ryanchaiyakul/potentiostat/CAD/LTSpice/Control Amp/ADA4622/Control Amp ADA4625 (Experimental).asc

R1: res; 10000
R2: res; 46392
U1: ADA4622
V1: voltage; 0
V2: voltage; 5
Named nets: 0, 5V, CE, DAC_OUT, RE
.dc V1 0 3.3 0.01
