ryanchaiyakul/potentiostat/CAD/LTSpice/Control Amp/ADA4622/Control AMP ADA4625 Transient (Experimental).asc

R1: res; 10000
R2: res; 46392
U1: ADA4622
V1: voltage; PWL file=swv.txt
V2: voltage; 5
Named nets: 0, 5V, CE, DAC_OUT, RE
.tran 0 9 0 0.01
