ryanchaiyakul/potentiostat/CAD/LTSpice/Control Amp/LT1462/Control Amp LT1462 Transients (Experimental).asc

R1: res; 10000
R2: res; 46392
U1: LT1462
V1: voltage; 3.3
V2: voltage; PWL file=swv.txt
Named nets: 0, 3.3V, RE, CE, DAC_OUT
.tran 0 9 0 0.01
