ryanchaiyakul/potentiostat/CAD/LTSpice/CPE/Randles Tester/cpe1.asc

C1: cap; 2.3655090766818945m
C2: cap; 1.4274608509243711m
C3: cap; 861.3978703391572u
C4: cap; 519.8085051119542u
C5: cap; 313.67721153099507u
C6: cap; 189.28777052747355u
C7: cap; 114.22525690145986u
C8: cap; 68.92896079787036u
C9: cap; 41.595018173372345u
C10: cap; 25.100415221937176u
C11: cap; 15.146786129233593u
C12: cap; 9.140292222904383u
C13: cap; 5.515687698187207u
C14: cap; 3.328428680616806u
C15: cap; 2.0085324057766334u
C16: cap; 1.212044124168307u
C17: cap; 731.405156673529n
C18: cap; 441.364709866243n
C19: cap; 671.6401428134171n
R1: res; 6.412486486066959meg
R2: res; 4.22741983895789meg
R3: res; 1.67962742799552meg
R4: res; 667.3451902923115k
R5: res; 265.14785099560146k
R6: res; 105.34785282080367k
R7: res; 41.856534202639345k
R8: res; 16.630329034202642k
R9: res; 6.607518970560247k
R10: res; 2.625282209180706k
R11: res; 1.043070282287264k
R12: res; 414.4299648952302
R13: res; 164.66023308270306
R14: res; 65.42237447937526
R15: res; 25.993447248248913
R16: res; 10.327648686314557
R17: res; 4.103354448114615
R18: res; 1.6303340903892138
R19: res; 647.760089920212m
Named nets: A, B
