ryanchaiyakul/potentiostat/CAD/LTSpice/CPE/Randles Tester/cpe2.asc

C1: cap; 181.21604919389156n
C2: cap; 163.35222877831924n
C3: cap; 147.24937865902783n
C4: cap; 132.73390683205375n
C5: cap; 119.64933355472706n
C6: cap; 107.85460446217489n
C7: cap; 97.22256997253973n
C8: cap; 87.63861458859019n
C9: cap; 78.9994213193171n
C10: cap; 71.21185790172778n
C11: cap; 64.19197281608272n
C12: cap; 57.8640902714143n
C13: cap; 52.15999440508718n
C14: cap; 47.01819390190557n
C15: cap; 42.383259105211465n
C16: cap; 38.20522447389643n
C17: cap; 34.43904994369196n
C18: cap; 31.044135386103342n
C19: cap; 283.8770536114015n
R1: res; 152.28690451341373g
R2: res; 55.18275033852288g
R3: res; 14.677500365520673g
R4: res; 3.9039195338813926g
R5: res; 1.03836398211393g
R6: res; 276.18390952836046meg
R7: res; 73.45935837169706meg
R8: res; 19.53871006314831meg
R9: res; 5.196903422435292meg
R10: res; 1.3822716594305113meg
R11: res; 367.6564263665744k
R12: res; 97.78920585287135k
R13: res; 26.009959558820995k
R14: res; 6.918125475621083k
R15: res; 1.8400820650336644k
R16: res; 489.42477525020337
R17: res; 130.17713458575
R18: res; 34.62449640048013
R19: res; 9.209418803093675
Named nets: A, B
