ryanchaiyakul/potentiostat/CAD/LTSpice/CPE/Randles Tester/randles.asc

R1: res; 230
R2: res; 37.785k
X1: cpe1
X2: cpe2
Named nets: A, B
