ryanchaiyakul/potentiostat/CAD/LTSpice/CPE/Randles Tester/Randles_Tester.asc

B1: bv; V=1-V(re)
V1: voltage; PWL file=swv.txt
X1: randles
Named nets: 0, RE, WE-RE
.tran 0 11 0 0.01
