ryanchaiyakul/potentiostat/CAD/LTSpice/System/Mixed System.asc

B1: bv; V=2*V(dac_we)-V(re)
V1: voltage; 5
V2: voltage; PWL file=swv.txt
V4: voltage; 2
X1: OPA2328_Control_Amp
X2: OPA2328_Trans_Amp; R=2k C=1.5n
X3: randles
Named nets: 0, 5V, DAC_OUT, CE, RE, WE-RE, WE-I, SIG_OUT, DAC_WE
.tran 0 11 0
