ryanchaiyakul/potentiostat/CAD/LTSpice/System/OPA2328_Control_Amp.asc

R1: res; 46392
R2: res; 10000
U1: opamp2; OPAx328
Named nets: V+, 0, DAC_OUT, RE, CE
.inc OPAx328.LIB
