ryanchaiyakul/potentiostat/CAD/LTSpice/System/OPA2328_Trans_Amp.asc

C1: cap; {C}
R1: res; {R}
U1: opamp2; OPAx328
Named nets: 0, V+, WE, I, SIG_OUT
.inc OPAx328.LIB
