ryanchaiyakul/potentiostat/CAD/LTSpice/System/OPA2392_System.asc

B1: bv; V=2*V(dac_we)-V(re)
Control: OPA2392_Control_Amp
Randles: Randles_Circuit
Transimpedance: OPA2392_Trans_Amp; R=47k C=17nF
V1: voltage; 5
V2: voltage; PWL file=swv.txt
V4: voltage; 1
Named nets: 0, 5V, DAC_OUT, CE, RE, WE-RE, WE-I, SIG_OUT, DAC_WE
.tran 0 11 0
