ryanchaiyakul/potentiostat/CAD/LTSpice/System/OPA2392_Trans_Amp.asc

C1: cap; {C}
R1: res; {R}
U1: opamp2; OPAx392
Named nets: 0, V+, WE, I, SIG_OUT
.inc OPAx392.LIB
