ryanchaiyakul/potentiostat/CAD/LTSpice/Control Amp/ADA4622/Control AMP ADA4625 Noise.asc

R1: res; {CERE}
R2: res; {REWE}
U1: ADA4622
V1: voltage; PWL file=swv.txt
V2: voltage; 5
Named nets: 0, 5V, CE, DAC_OUT, RE
.step param REWE  list 5000 10000 100000
.step param CERE  list 1 1000 5000
.noise V(RE) V2 oct 100 100 100000
;tran 0 9 0 0.01
