ryanchaiyakul/potentiostat/CAD/LTSpice/Control Amp/LT1462/Control Amp LT1462 Transients.asc

R1: res; {C}
R2: res; {R}
U1: LT1462
V1: voltage; 3.3
V2: voltage; PWL file=swv.txt
Named nets: 0, 3.3V, RE, CE, DAC_OUT
.step param R list 5000 10000 100000
.step param C list 1 1000 5000
.tran 0 9 0 0.01
