ryanchaiyakul/potentiostat/CAD/LTSpice/Control Amp/OPA2392/OPA2392_Control_Amp.asc

R1: res; 46392
R2: res; 10000
U1: opamp2; OPAx392
Named nets: V+, 0, DAC_OUT, RE, CE
.inc OPAx392.LIB
