ryanchaiyakul/potentiostat/CAD/LTSpice/Trans Amp/LT1462/CPE1.asc

C1: cap; 93.371n
C2: cap; 84.112n
C3: cap; 75.771n
C4: cap; 68.257n
C5: cap; 61.489n
C6: cap; 55.391n
C7: cap; 49.898n
C8: cap; 44.95n
C9: cap; 40.493n
C10: cap; 36.477n
C11: cap; 331.37n
R1: res; 10.71Meg
R2: res; 2.8251Meg
R3: res; 745.21k
R4: res; 196.57k
R5: res; 51.852k
R6: res; 13.678k
R7: res; 3.6079k
R8: res; 951.69
R9: res; 251.04
R10: res; 66.219
R11: res; 29.892Meg
Named nets: A, B
