ryanchaiyakul/potentiostat/CAD/LTSpice/Trans Amp/LT1462/CPE2.asc

C1: cap; 91.575µ
C2: cap; 55.086µ
C3: cap; 33.137µ
C4: cap; 19.933µ
C5: cap; 11.99µ
C6: cap; 7.2128µ
C7: cap; 4.3388µ
C8: cap; 2.6099µ
C9: cap; 1.57µ
C10: cap; 944.41n
C11: cap; 1.4257µ
R1: res; 10.92k
R2: res; 4.3137k
R3: res; 1.704k
R4: res; 673.13
R5: res; 265.9
R6: res; 105.04
R7: res; 41.493
R8: res; 16.391
R9: res; 6.4748
R10: res; 2.5577
R11: res; 16.724k
Named nets: A, B
