ryanchaiyakul/potentiostat/CAD/LTSpice/Trans Amp/LT1462/Trans Amp LT1462 Transient.asc

C1: cap; 0.1µ; V=4 Irms=0 Rser=0 Lser=0 mfg="Murata" pn="GRM022R60G153KE15" type="X5R"
C2: cap; 0.1µ; V=4 Irms=0 Rser=0 Lser=0 mfg="Murata" pn="GRM022R60G153KE15" type="X5R"
R1: res; {X}; tol=1 pwr=0.1
R2: res; 1K; tol=1 pwr=0.1
U1: LT1462
V1: voltage; 3.3
V2: voltage; 1
V3: voltage; PWL file=swv.txt
X1: Randles_Circuit
Named nets: 0, 1V, 3.3V, 2V, SIG_OUT, WE-RE
.step param X list 1000 2200 4700 10000 22000 47000
.tran 0 11 0 0.001
