ryanchaiyakul/potentiostat/CAD/LTSpice/Trans Amp/OPA2392/OPA2392_Trans_Amp AC.asc

C1: cap; 1.5n; V=50
C2: cap; 1T
L1: ind; 1T
R1: res; 2k
U1: opamp2; OPAx328
U2: LT1462
V1: voltage; 5
V4: voltage; ac 1
X1: Randles_Circuit
Named nets: SIG_OUT, 0, V+, FB
.inc OPAx392.LIB
.ac dec 101 1 100k
.inc OPAx328.LIB
