ryanchaiyakul/potentiostat/CAD/LTSpice/Trans Amp/OPA2392/OPA2392_Trans_Amp.asc

C1: cap
R1: res
U1: opamp2; OPAx392
Named nets: 0, V+, WE, I, SIG_OUT
.inc OPAx392.LIB
