ryanchaiyakul/potentiostat/CAD/LTSpice/Trans Amp/LT1462/Randles_Circuit.asc

R3: res; 37785
R4: res; 230
X1: CPE1
X2: CPE2
Named nets: WE, WE-RE
