ryanchaiyakul/potentiostat/CAD/LTSpice/Trans Amp/LT1462/Trans Amp LT1462.asc

C1: cap; 0.1µ; V=4 Irms=0 Rser=0 Lser=0 mfg="Murata" pn="GRM022R60G153KE15" type="X5R"
C2: cap; 0.1µ; V=4 Irms=0 Rser=0 Lser=0 mfg="Murata" pn="GRM022R60G153KE15" type="X5R"
I1: current; 0
R1: res; {X}; tol=1 pwr=0.1
R2: res; 1K; tol=1 pwr=0.1
U1: LT1462
V1: voltage; 3.3
V2: voltage; 2
Named nets: 0, 2V, 3.3V, I, SIG_OUT
.dc I1 -0.001 0.001 0.0000001
.step param X list 1000 2200 4700 10000 22000 47000
