ryanchaiyakul/potentiostat/CAD/LTSpice/CPE/Paper/Paper CPE.asc

C1: cap; 1µ
C2: cap; 542.8n
C3: cap; 294.7n
C4: cap; 160n
C5: cap; 86.9n
C6: cap; 103.2n
I1: current; AC 1
R1: res; 10k
R2: res; 2947
R3: res; 869
R4: res; 256
R5: res; 75.4
R6: res; 23.9k
Named nets: 0, V1
.ac dec 100 1 1meg
